mc-cat-tty/DoorbellCamPhy/NotifierPcb/Exports/NotifierPcbExtrusion.stl

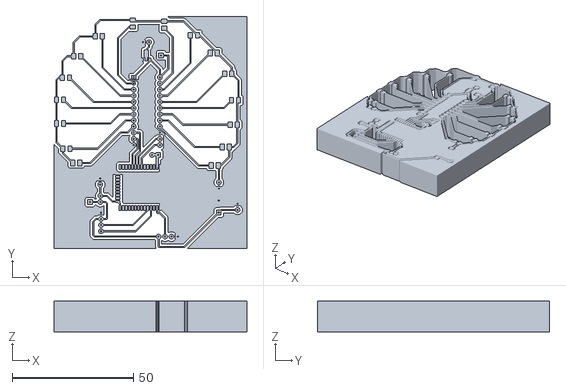
[picture p34: CAD file, 2022-08-07]
NotifierPcb/Exports/NotifierPcbExtrusion.stl
79.6 x 95.9 x 12.6
