mc-cat-tty/DoorbellCamPhy/NotifierPcb/Exports/NotifierPcbFlatMirrored.stl

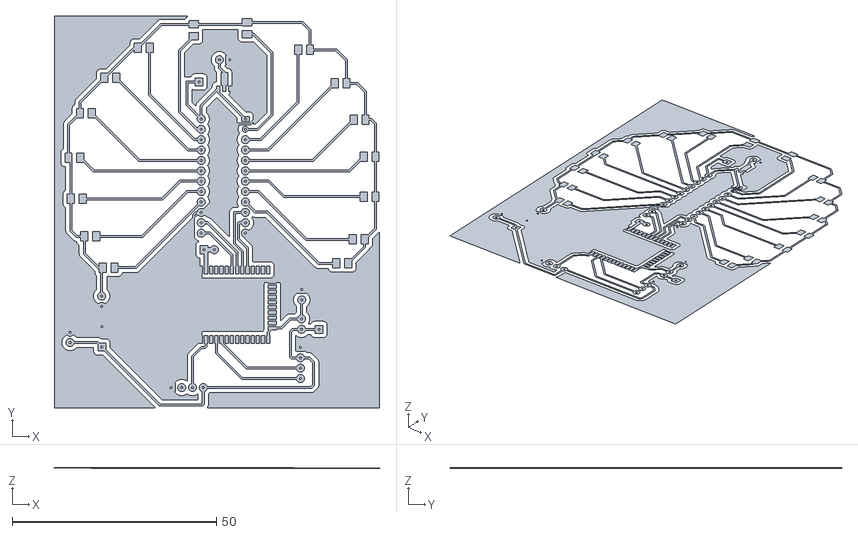
[picture p35: CAD file, 2022-08-07]
NotifierPcb/Exports/NotifierPcbFlatMirrored.stl
79.6 x 95.9 x 2.72e-05
